NathanWeasley/bedside_weather/App/graphics/gfx_paint.hpp

#pragma once

#include "graphics/gfx_animated.hpp"
#include "graphics/gfx_fonts.h"

namespace gfx
{

typedef enum : uint8_t
{
    DOT_FILL_AROUND = 1,
    DOT_FILL_RIGHTUP
} dot_fill_e;

typedef enum : uint8_t
{
    DOT_SIZE_1 = 1,
    DOT_SIZE_2,
    DOT_SIZE_3,
    DOT_SIZE_4,
    DOT_SIZE_5,
    DOT_SIZE_6,
    DOT_SIZE_7,
    DOT_SIZE_8
} dot_size_e;

typedef enum : uint8_t
{
    LINE_SOLID = 0,
    LINE_DOTTED
} line_style_e;

typedef enum : uint8_t
{
    SHAPE_FILL = 1,
    SHAPE_NOFILL = 0
} shape_fill_e;



template <typename T>
static inline void set_whole(uint8_t color)
{
    if constexpr (is_Canvas_v<T>)
    {
        memset(T::data(), color, T::size());
    }
    else if constexpr (is_Window_v<T>)
    {
        for (uint16_t i = 0; i < T::height(); ++i)
        {
            uint8_t * ptr = T::data() + T::canvas().width() * i;
            memset(ptr, color, T::width());
        }
    }
}

template <typename T, typename = std::enable_if_t<is_Window_v<T>>>
static inline void draw_px(uint16_t x, uint16_t y, uint8_t color)
{
    if (x >= T::width() || y >= T::height())
        return;

    T::data()[x + T::canvas().width()*y] = color;
}

template <typename T, typename = std::enable_if_t<is_Window_v<T>>>
void draw_pt(uint16_t x, uint16_t y, uint16_t color, uint8_t size, dot_fill_e fill = DOT_FILL_AROUND)
{
    if (x >= T::width() || y >= T::height())
    {
        return;
    }

    int16_t XDir_Num , YDir_Num;
    if (fill == DOT_FILL_AROUND)
    {
        for (XDir_Num = 0; XDir_Num < 2 * size - 1; ++XDir_Num)
        {
            for (YDir_Num = 0; YDir_Num < 2 * size - 1; ++YDir_Num)
            {
                if(x + XDir_Num - size < 0 || y + YDir_Num - size < 0)
                    break;

                draw_px<T>(x + XDir_Num - size, y + YDir_Num - size, color);
            }
        }
    }
    else
    {
        for (XDir_Num = 0; XDir_Num < size; XDir_Num++)
        {
            for (YDir_Num = 0; YDir_Num < size; YDir_Num++)
            {
                draw_px<T>(x + XDir_Num - 1, y + YDir_Num - 1, color);
            }
        }
    }
}

template <typename T, typename = std::enable_if_t<is_Window_v<T>>>
static inline void draw_line(uint16_t x0, uint16_t y0, uint16_t x1, uint16_t y1, uint8_t color, uint8_t width, line_style_e style)
{
    if (x0 >= T::width() || y0 >= T::height() || x1 >= T::width() || y1 >= T::height())
        return;

    uint16_t Xpoint = x0;
    uint16_t Ypoint = y0;
    int dx = (int)x1 - (int)x0 >= 0 ? x1 - x0 : x0 - x1;
    int dy = (int)y1 - (int)y0 <= 0 ? y1 - y0 : y0 - y1;

    // Increment direction, 1 is positive, -1 is counter;
    int XAddway = x0 < x1 ? 1 : -1;
    int YAddway = y0 < y1 ? 1 : -1;

    //Cumulative error
    int Esp = dx + dy;
    uint8_t Dotted_Len = 0;

    for (;;)
    {
        ++Dotted_Len;
        //Painted dotted line, 2 point is really virtual
        if (style == LINE_DOTTED && Dotted_Len % 3 == 0)
        {
            // draw_pt<T>(Xpoint, Ypoint, 0, width);
            Dotted_Len = 0;
        }
        else
        {
            draw_pt<T>(Xpoint, Ypoint, color, width);
        }

        if (2 * Esp >= dy)
        {
            if (Xpoint == x1)
                break;
            Esp += dy;
            Xpoint += XAddway;
        }
        if (2 * Esp <= dx)
        {
            if (Ypoint == y1)
                break;
            Esp += dx;
            Ypoint += YAddway;
        }
    }
}

template <typename T, typename = std::enable_if_t<is_Window_v<T>>>
void draw_rectangle(uint16_t x0, uint16_t y0, uint16_t x1, uint16_t y1,
                         uint16_t color, uint8_t width, shape_fill_e fill)
{
    if (x0 > T::width() || y0 > T::height() || x1 > T::width() || y1 > T::height())
    {
        return;
    }

    if (fill)
    {
        uint16_t Ypoint;
        for(Ypoint = y0; Ypoint <= y1; Ypoint++)
        {
            draw_line<T>(x0, Ypoint, x1, Ypoint, color, width, LINE_SOLID);
        }
    }
    else
    {
        draw_line<T>(x0, y0, x1, y0, color, width, LINE_SOLID);
        draw_line<T>(x0, y0, x0, y1, color, width, LINE_SOLID);
        draw_line<T>(x1, y1, x1, y0, color, width, LINE_SOLID);
        draw_line<T>(x1, y1, x0, y1, color, width, LINE_SOLID);
    }
}

template <typename T, typename = std::enable_if_t<is_Window_v<T>>>
void draw_circle(uint16_t x, uint16_t y, uint16_t r, uint16_t color, uint8_t width, shape_fill_e fill)
{
    if (x > T::width() || y >= T::height())
    {
        return;
    }

    //Draw a circle from(0, R) as a starting point
    int16_t XCurrent, YCurrent;
    XCurrent = 0;
    YCurrent = r;

    //Cumulative error,judge the next point of the logo
    int16_t Esp = 3 - (r << 1);

    int16_t sCountY;
    if (fill == SHAPE_FILL)
    {
        while (XCurrent <= YCurrent)
        { //Realistic circles
            for (sCountY = XCurrent; sCountY <= YCurrent; ++sCountY)
            {
                draw_pt<T>(x + XCurrent, y + sCountY, color, 1);//1
                draw_pt<T>(x - XCurrent, y + sCountY, color, 1);//2
                draw_pt<T>(x - sCountY, y + XCurrent, color, 1);//3
                draw_pt<T>(x - sCountY, y - XCurrent, color, 1);//4
                draw_pt<T>(x - XCurrent, y - sCountY, color, 1);//5
                draw_pt<T>(x + XCurrent, y - sCountY, color, 1);//6
                draw_pt<T>(x + sCountY, y - XCurrent, color, 1);//7
                draw_pt<T>(x + sCountY, y + XCurrent, color, 1);
            }
            if (Esp < 0)
            {
                Esp += 4 * XCurrent + 6;
            }
            else
            {
                Esp += 10 + 4 * (XCurrent - YCurrent);
                --YCurrent;
            }
            ++XCurrent;
        }
    }
    else
    { //Draw a hollow circle
        while (XCurrent <= YCurrent)
        {
            draw_pt<T>(x + XCurrent, y + YCurrent, color, width);   //1
            draw_pt<T>(x - XCurrent, y + YCurrent, color, width);   //2
            draw_pt<T>(x - YCurrent, y + XCurrent, color, width);   //3
            draw_pt<T>(x - YCurrent, y - XCurrent, color, width);   //4
            draw_pt<T>(x - XCurrent, y - YCurrent, color, width);   //5
            draw_pt<T>(x + XCurrent, y - YCurrent, color, width);   //6
            draw_pt<T>(x + YCurrent, y - XCurrent, color, width);   //7
            draw_pt<T>(x + YCurrent, y + XCurrent, color, width);   //0

            if (Esp < 0)
            {
                Esp += 4 * XCurrent + 6;
            }
            else
            {
                Esp += 10 + 4 * (XCurrent - YCurrent);
                --YCurrent;
            }
            ++XCurrent;
        }
    }
}

template <typename T, typename F, typename = std::enable_if_t<is_Window_v<T>>>
uint16_t draw_char(uint16_t x, uint16_t y, const char ch_ascii,
                   const F& ft, uint16_t color_fg, int16_t color_bg = -1)
{
    static_assert(is_Font_v<F>, "Unsupported font type!");

    if (x > T::width() || y > T::height())
    {
        return x;
    }

    uint8_t ch_idx = ch_ascii - F::ascii_bias();
    // const auto& ch_bmp = ft.glyphs[ch_idx];
    const uint8_t * ptr = ft.data(ch_idx);

    for (uint16_t Row = 0; Row < ft.height(); ++Row)
    {
        const uint8_t * rptr = ptr + ft.widthByte() * Row;

        for (uint16_t Column = 0; Column < ft.width(ch_idx); ++Column)
        {
            // To determine whether the font background color and screen background color is consistent
            if (color_bg < 0)
            {
                // this process is to speed up the scan
                if (*rptr & (0x80 >> (Column % 8)))
                {
                    draw_px<T>(x + Column, y + Row, color_fg);
                    // Paint_DrawPoint(x + Column, y + Row, color_fg, DOT_PIXEL_DFT, DOT_STYLE_DFT);
                }
            }
            else
            {
                if (*rptr & (0x80 >> (Column % 8)))
                {
                    draw_px<T>(x + Column, y + Row, color_fg);
                    // Paint_DrawPoint(x + Column, y + Row, color_fg, DOT_PIXEL_DFT, DOT_STYLE_DFT);
                }
                else
                {
                    draw_px<T>(x + Column, y + Row, color_bg);
                    // Paint_DrawPoint(x + Column, y + Row, color_bg, DOT_PIXEL_DFT, DOT_STYLE_DFT);
                }
            }
            // One pixel is 8 bits
            if (Column % 8 == 7)
            {
                rptr++;
            }
        } // Write a line
    } // Write all

    return x + ft.width(ch_idx);
}

template <typename T, typename F, typename = std::enable_if_t<is_Window_v<T>>>
uint16_t draw_string(uint16_t x, uint16_t y, const char * str,
                 const F& ft, uint16_t color_fg, int16_t color_bg = -1)
{
    static_assert(is_Font_v<F>, "Unsupported font type!");

    uint16_t Xpoint = x;
    uint16_t Ypoint = y;

    if (x > T::width() || y > T::height())
    {
        return x;
    }

    while (*str != '\0')
    {
        uint8_t ch_idx = *str - F::ascii_bias();
        uint16_t ch_width = ft.width(ch_idx);

        //if X direction overflowed, reposition to (x,Ypoint), Ypoint is Y direction plus the Height of the character
        if (Xpoint + ch_width > T::width())
        {
            Xpoint = x;
            Ypoint += ft.height();
        }

        // If Y direction overflowed, reposition to (x, y)
        if (Ypoint + ft.height() > T::height())
        {
            Xpoint = x;
            Ypoint = y;
        }

        Xpoint = draw_char<T, F>(Xpoint, Ypoint, *str, ft, color_fg, color_bg);

        //The next character of the address
        ++str;

        // //The next word of the abscissa increases the font of the broadband
        // Xpoint += ft.width(ch_idx);
    }

    return Xpoint;
}

template <typename T, typename F, typename = std::enable_if_t<is_Window_v<T>>>
uint16_t draw_number(uint16_t x, uint16_t y, int32_t num,
                     const F& ft, uint16_t color_fg, int16_t color_bg = -1)
{
    static_assert(is_Font_v<F>, "Unsupported font type!");

    if (x > T::width() || y > T::height())
    {
        return x;
    }

    static constexpr uint32_t __array_len = 128;

    int16_t Num_Bit = 0, Str_Bit = 0;
    uint8_t Str_Array[__array_len] = {0}, Num_Array[__array_len] = {0};
    uint8_t *pStr = Str_Array;
    uint8_t neg;

    neg = num < 0;
    if (neg)
    {
        num = -num;
    }

    // Converts a number to a string
    do
    {
        Num_Array[Num_Bit] = num % 10 + '0';
        ++Num_Bit;
        num /= 10;
    } while (num);
    
    // Adds minus sign if number is negative
    if (neg)
    {
        Str_Array[0] = '-';
        ++Str_Bit;
    }

    // The string is inverted
    while (Num_Bit > 0)
    {
        Str_Array[Str_Bit] = Num_Array[Num_Bit - 1];
        ++Str_Bit;
        --Num_Bit;
    }

    return draw_string<T, F>(x, y, (const char*)pStr, ft, color_fg, color_bg);
}

// template <typename T, typename = std::enable_if_t<is_Window_v<T>>>
// void draw_bitmap(const uint8_t* image_buffer)
// {
//     uint16_t x, y;
//     uint32_t Addr = 0;



//     for (y = 0; y < Paint.HeightByte; y++) {
//         for (x = 0; x < Paint.WidthByte; x++) {//8 pixel =  1 byte
//             Addr = x + y * Paint.WidthByte;
//             Paint.Image[Addr] = (unsigned char)image_buffer[Addr];
//         }
//     }
// }













#if 0

template <typename T>
static inline void dump(const char * path)
{
    FILE * fid = fopen(path, "w");
    if (fid)
    {
        fwrite(T::data(), T::size(), 1, fid);

        fclose(fid);
    }
}

#endif

}
