NathanWeasley/bedside_weather/App/graphics/icon_5.c

#include "graphics/icon_5.h"

/**
 * Total 95 ASCII characters
 *
 *  !"#$%&'()*+,-./
 * 0123456789:;<=>?
 * @ABCDEFGHIJKLMNO
 * PQRSTUVWXYZ[\]^_
 * `abcdedfhijklmno
 * pqrstuvwxyz{|}~
*/

static const icon_5_font_t g_font5 =
{
    ICON_5_HEIGHT,
    {
        { 4, { 0x00, 0x00, 0x00, 0x00, 0x00, } },       ///< ' '
        { 4, { 0x40, 0x40, 0x40, 0x00, 0x40, } },       ///< '!'
        { 4, { 0xA0, 0xA0, 0x00, 0x00, 0x00, } },       ///< '\"'
        { 6, { 0x50, 0xF8, 0x50, 0xF8, 0x50, } },       ///< '#'
        { 4, { 0xE0, 0xC0, 0xE0, 0x60, 0xE0, } },       ///< '$'
        { 4, { 0x80, 0x20, 0x40, 0x80, 0x20, } },       ///< '%'
        { 6, { 0x60, 0xA0, 0x68, 0x90, 0x68, } },       ///< '&'
        { 4, { 0x40, 0x40, 0x00, 0x00, 0x00, } },       ///< '\''
        { 4, { 0x20, 0x40, 0x40, 0x40, 0x20, } },       ///< '('
        { 4, { 0x80, 0x40, 0x40, 0x40, 0x80, } },       ///< ')'
        { 4, { 0x40, 0xE0, 0x40, 0xA0, 0x00, } },       ///< '*'
        { 4, { 0x00, 0x40, 0xE0, 0x40, 0x00, } },       ///< '+'
        { 4, { 0x00, 0x00, 0x00, 0x40, 0xC0, } },       ///< ','
        { 4, { 0x00, 0x00, 0xE0, 0x00, 0x00, } },       ///< '-'
        { 4, { 0x00, 0x00, 0x00, 0x00, 0x40, } },       ///< '.'
        { 4, { 0x00, 0x20, 0x40, 0x80, 0x00, } },       ///< '/'

        { 4, { 0x40, 0xA0, 0xA0, 0xA0, 0x40, } },       ///< '0'
        { 4, { 0x40, 0xC0, 0x40, 0x40, 0xE0, } },       ///< '1'
        { 4, { 0xE0, 0x20, 0xE0, 0x80, 0xE0, } },       ///< '2'
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

        { 4, { 0x60, 0x40, 0xC0, 0x40, 0x60, } },       ///< '{'
        { 4, { 0x40, 0x40, 0x40, 0x40, 0x40, } },       ///< '|'
        { 4, { 0xC0, 0x40, 0x60, 0x40, 0xC0, } },       ///< '}'
        { 5, { 0x00, 0x50, 0xA0, 0x00, 0x00, } },       ///< '~'
    }
};
