NathanWeasley/bedside_weather/Core/Inc/rtc.h

#pragma once

#ifdef __cplusplus
extern "C" {
#endif

#include "main.h"

typedef struct
{
    uint8_t year;       /* 0..99，对应 2000..2099 */
    uint8_t month;
    uint8_t day;
    uint8_t hour;
    uint8_t minute;
    uint8_t second;
    uint8_t weekday;
} date_time_t;

void MX_RTC_Init(void);

void MX_RTC_Get(date_time_t * pdatetime);
void MX_RTC_Set(const date_time_t * pdatetime);

#ifdef __cplusplus
}
#endif
