NathanWeasley/bedside_weather/App/graphics/icon_16.cpp

#include "graphics/icon_16.h"

namespace gfx
{

const Icon16 icon16_table =
{
    {
        {
            {
                0xFF, 0xFF,
                0xFF, 0xFF,
                0xFF, 0xFF,
                0xFF, 0xFF,
                0xFF, 0xFF,
                0xFF, 0xFF,
                0xFF, 0xFF,
                0xFF, 0xFF,
                0xFF, 0xFF,
                0xFF, 0xFF,
                0xFF, 0xFF,
                0xFF, 0xFF,
                0xFF, 0xFF,
                0xFF, 0xFF,
                0xFF, 0xFF,
                0xFF, 0xFF,
            }
        },
        {
            {
                0x55, 0xFF,
                0x55, 0xFF,
                0x55, 0xFF,
                0x55, 0xFF,
                0x55, 0xFF,
                0x55, 0xFF,
                0x55, 0xFF,
                0x55, 0xFF,
                0x55, 0xFF,
                0x55, 0xFF,
                0x55, 0xFF,
                0x55, 0xFF,
                0x55, 0xFF,
                0x55, 0xFF,
                0x55, 0xFF,
                0x55, 0xFF,
            }
        }
    }
};

}
