NathanWeasley/bedside_weather/Core/Inc/usart.h

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
/* Define to prevent recursive inclusion -------------------------------------*/
#ifndef __USART_H__
#define __USART_H__

#ifdef __cplusplus
extern "C" {
#endif

/* Includes ------------------------------------------------------------------*/
#include "main.h"

void MX_USART1_UART_Init(void);

/* USER CODE BEGIN Prototypes */

void MX_USART1_UART_StartReceive(void);
uint8_t MX_USART1_UART_CheckTXAvailability(void);
/* data必须在DMA发送完成前保持有效；协议包使用此接口。 */
uint8_t MX_USART1_UART_TryDMASend(const uint8_t * data, uint16_t len);
/* 复制到内部64字节缓冲区；普通文本和调试信息使用此接口。 */
uint8_t MX_USART1_UART_DMASend(const uint8_t * data, uint16_t len);
void MX_USART1_UART_Send(const uint8_t * data, uint16_t len);

uint16_t MX_USART1_UART_GetReceived(uint8_t * buf, uint16_t maxlen);
uint32_t MX_USART1_UART_GetRxOverrunCount(void);
uint32_t MX_USART1_UART_GetRxErrorCount(void);
void MX_USART1_UART_RxDmaIRQHandler(void);

/* USER CODE END Prototypes */

#ifdef __cplusplus
}
#endif

#endif /* __USART_H__ */
