NathanWeasley/bedside_weather/Core/Src/timer.c

#include "main.h"
#include "config.h"

void MX_TIM3_Init(void)
{
    LL_TIM_InitTypeDef TIM_InitStruct = {0};

    LL_APB1_GRP1_EnableClock(LL_APB1_GRP1_PERIPH_TIM3);

    NVIC_SetPriority(TIM3_IRQn, 0);
    NVIC_EnableIRQ(TIM3_IRQn);

    TIM_InitStruct.Prescaler = 64U - 1U;      /* 1MHz，计数单位1us */
    TIM_InitStruct.CounterMode = LL_TIM_COUNTERDIRECTION_UP;
    TIM_InitStruct.Autoreload = 25U - 1U;
    TIM_InitStruct.ClockDivision = LL_TIM_CLOCKDIVISION_DIV1;
    LL_TIM_Init(TIM3, &TIM_InitStruct);
    LL_TIM_DisableARRPreload(TIM3);
    LL_TIM_SetClockSource(TIM3, LL_TIM_CLOCKSOURCE_INTERNAL);
    LL_TIM_EnableIT_UPDATE(TIM3);
    LL_TIM_ClearFlag_UPDATE(TIM3);
}

void MX_TIM6_Init(void)
{
    LL_TIM_InitTypeDef TIM_InitStruct = {0};

    LL_APB1_GRP1_EnableClock(LL_APB1_GRP1_PERIPH_TIM6);

    NVIC_SetPriority(TIM6_IRQn, 2);
    NVIC_EnableIRQ(TIM6_IRQn);

    TIM_InitStruct.Prescaler = 64 - 1;      //< 1MHz clock (1us)
    TIM_InitStruct.CounterMode = LL_TIM_COUNTERDIRECTION_UP;
    TIM_InitStruct.Autoreload = TASK_SCHEDULE_PERIOD_US - 1;
    TIM_InitStruct.ClockDivision = LL_TIM_CLOCKDIVISION_DIV1;
    LL_TIM_Init(TIM6, &TIM_InitStruct);
    LL_TIM_EnableARRPreload(TIM6);
    LL_TIM_SetClockSource(TIM6, LL_TIM_CLOCKSOURCE_INTERNAL);
    LL_TIM_SetTriggerOutput(TIM6, LL_TIM_TRGO_RESET);
    LL_TIM_DisableMasterSlaveMode(TIM6);
    LL_TIM_EnableIT_UPDATE(TIM6);

    LL_TIM_ClearFlag_UPDATE(TIM6);
    LL_TIM_EnableCounter(TIM6);
}
