NathanWeasley/bedside_weather/App/graphics/icon_16.c

#include "graphics/icon_16.h"

static const icon_16_font_t g_font16 =
{
    ICON_16_HEIGHT,
    {
        {
            16,
            {
                0xFF, 0xFF,
                0xFF, 0xFF,
                0xFF, 0xFF,
                0xFF, 0xFF,
                0xFF, 0xFF,
                0xFF, 0xFF,
                0xFF, 0xFF,
                0xFF, 0xFF,
                0xFF, 0xFF,
                0xFF, 0xFF,
                0xFF, 0xFF,
                0xFF, 0xFF,
                0xFF, 0xFF,
                0xFF, 0xFF,
                0xFF, 0xFF,
                0xFF, 0xFF,
            }
        },
        {
            8,
            {
                0x55, 0xFF,
                0x55, 0xFF,
                0x55, 0xFF,
                0x55, 0xFF,
                0x55, 0xFF,
                0x55, 0xFF,
                0x55, 0xFF,
                0x55, 0xFF,
                0x55, 0xFF,
                0x55, 0xFF,
                0x55, 0xFF,
                0x55, 0xFF,
                0x55, 0xFF,
                0x55, 0xFF,
                0x55, 0xFF,
                0x55, 0xFF,
            }
        }
    }
};
