NathanWeasley/bedside_weather/App/graphics/demo_img.c

#include <stdint.h>

const uint8_t g_test_img[] =
{
 54, 60, 66, 69, 72, 74, 75, 74, 72, 69, 66, 60, 54, 47, 40, 34, 28, 22, 18, 13, 9, 6, 4, 2, 1,
 63, 70, 76, 81, 85, 86, 87, 86, 85, 81, 76, 70, 63, 55, 47, 39, 255, 26, 20, 255, 11, 8, 5, 3, 1,
 71, 79, 86, 91, 95, 98, 98, 98, 95, 91, 86, 79, 255, 255, 255, 255, 255, 255, 255, 255, 255, 255, 255, 255, 1,
 78, 87, 95, 101, 105, 107, 108, 107, 105, 101, 95, 87, 78, 68, 58, 48, 255, 42, 25, 255, 14, 9, 6, 3, 2,
 84, 94, 102, 202, 202, 110, 110, 110, 202, 202, 102, 94, 84, 73, 62, 52, 43, 35, 255, 255, 255, 255, 255, 3, 2,
 88, 98, 207, 235, 215, 202, 110, 202, 202, 202, 202, 98, 88, 255, 255, 255, 255, 36, 255, 22, 16, 11, 255, 4, 2,
 91, 101, 230, 248, 207, 202, 202, 202, 202, 202, 202, 101, 91, 255, 67, 56, 255, 37, 255, 22, 16, 11, 255, 4, 2,
 91, 102, 224, 217, 202, 202, 202, 202, 202, 202, 202, 102, 91, 255, 255, 255, 255, 38, 255, 255, 255, 255, 255, 4, 2,
 91, 101, 202, 202, 202, 202, 202, 202, 194, 200, 202, 101, 91, 255, 67, 57, 255, 37, 255, 22, 16, 11, 255, 4, 2,
 89, 99, 108, 202, 202, 202, 202, 180, 176, 197, 108, 99, 88, 255, 66, 55, 255, 36, 255, 255, 255, 255, 255, 3, 2,
 85, 95, 104, 110, 202, 202, 184, 170, 194, 110, 104, 95, 85, 255, 255, 255, 255, 34, 255, 20, 14, 9, 255, 3, 2,
 80, 89, 97, 104, 109, 202, 201, 201, 109, 104, 97, 89, 80, 255, 59, 49, 255, 32, 255, 19, 13, 9, 255, 3, 1,
 73, 82, 90, 96, 101, 104, 202, 103, 101, 96, 90, 82, 73, 64, 54, 45, 37, 255, 22, 16, 12, 8, 255, 3, 1,
 66, 74, 81, 86, 91, 93, 94, 93, 91, 86, 81, 74, 66, 57, 48, 40, 255, 26, 20, 15, 10, 255, 255, 2, 1,
 57, 65, 71, 76, 79, 82, 83, 82, 79, 76, 71, 65, 57, 50, 42, 35, 28, 22, 17, 13, 9, 6, 3, 2, 1,
 49, 55, 60, 65, 68, 70, 71, 70, 68, 65, 60, 55, 49, 43, 36, 30, 24, 19, 14, 10, 7, 5, 3, 2, 1
};
